paulh002/ESP32Controler/FreeSansOblique.cpp

#include "lvgl.h"

/*******************************************************************************
 * Size: 42 px
 * Bpp: 1
 * Opts: 
 ******************************************************************************/

#ifndef FREESANSOBLIQUE
#define FREESANSOBLIQUE 1
#endif

#if FREESANSOBLIQUE

/*-----------------
 *    BITMAPS
 *----------------*/

/*Store the image of the glyphs*/
static LV_ATTRIBUTE_LARGE_CONST const uint8_t gylph_bitmap[] = {
    /* U+2C "," */
    0x3e, 0x7c, 0xf1, 0xe0, 0xc1, 0x82, 0xc, 0x31,
    0xc0,

    /* U+2E "." */
    0xff, 0xfd, 0xe0,

    /* U+30 "0" */
    0x0, 0x1f, 0x80, 0x7, 0xfe, 0x0, 0x7f, 0xf8,
    0x7, 0xc3, 0xe0, 0x78, 0xf, 0x83, 0x80, 0x3c,
    0x3c, 0x1, 0xe3, 0xc0, 0xf, 0x1e, 0x0, 0x78,
    0xe0, 0x3, 0xcf, 0x0, 0x1e, 0x78, 0x0, 0xf3,
    0x80, 0x7, 0xbc, 0x0, 0x3d, 0xe0, 0x1, 0xef,
    0x0, 0xe, 0x70, 0x0, 0xf3, 0x80, 0x7, 0xbc,
    0x0, 0x3d, 0xe0, 0x1, 0xcf, 0x0, 0x1e, 0x78,
    0x0, 0xf3, 0xc0, 0xf, 0x1e, 0x0, 0x78, 0xf0,
    0x7, 0x87, 0x80, 0x3c, 0x1e, 0x3, 0xc0, 0xf8,
    0x7c, 0x3, 0xff, 0xc0, 0xf, 0xfc, 0x0, 0x1f,
    0x80, 0x0,

    /* U+31 "1" */
    0x0, 0x70, 0x7, 0x0, 0xf0, 0xe, 0x1, 0xe0,
    0x7e, 0x3f, 0xef, 0xfc, 0xff, 0xcf, 0xfc, 0x3,
    0xc0, 0x3c, 0x3, 0x80, 0x38, 0x7, 0x80, 0x78,
    0x7, 0x80, 0x70, 0xf, 0x0, 0xf0, 0xf, 0x0,
    0xf0, 0xe, 0x1, 0xe0, 0x1e, 0x1, 0xe0, 0x1e,
    0x1, 0xc0, 0x3c, 0x3, 0xc0, 0x3c, 0x0,

    /* U+32 "2" */
    0x0, 0x7, 0xf0, 0x0, 0xf, 0xfe, 0x0, 0x1f,
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
    0x0, 0x0, 0x78, 0x0, 0x3, 0xc0, 0x0, 0x1e,
    0x0, 0x0, 0xf0, 0x0, 0x7, 0x80, 0x0, 0x3c,
    0x0, 0x1, 0xe0, 0x0, 0xf, 0x0, 0x0, 0xf8,
    0x0, 0x7, 0xc0, 0x0, 0x1f, 0xff, 0xf8, 0x7f,
    0xff, 0xe3, 0xff, 0xff, 0x0
};


/*---------------------
 *  GLYPH DESCRIPTION
 *--------------------*/

static const lv_font_fmt_txt_glyph_dsc_t glyph_dsc[] = {
    {.bitmap_index = 0, .adv_w = 0, .box_w = 0, .box_h = 0, .ofs_x = 0, .ofs_y = 0} /* id = 0 reserved */,
    {.bitmap_index = 0, .adv_w = 187, .box_w = 7, .box_h = 10, .ofs_x = 2, .ofs_y = -6},
    {.bitmap_index = 9, .adv_w = 187, .box_w = 5, .box_h = 4, .ofs_x = 4, .ofs_y = 0},
    {.bitmap_index = 12, .adv_w = 374, .box_w = 21, .box_h = 31, .ofs_x = 4, .ofs_y = -1},
    {.bitmap_index = 94, .adv_w = 374, .box_w = 12, .box_h = 31, .ofs_x = 9, .ofs_y = 0},
    {.bitmap_index = 141, .adv_w = 374, .box_w = 25, .box_h = 30, .ofs_x = 1, .ofs_y = 0},
    {.bitmap_index = 235, .adv_w = 374, .box_w = 22, .box_h = 31, .ofs_x = 3, .ofs_y = -1},
    {.bitmap_index = 321, .adv_w = 374, .box_w = 21, .box_h = 30, .ofs_x = 3, .ofs_y = 0},
    {.bitmap_index = 400, .adv_w = 374, .box_w = 23, .box_h = 31, .ofs_x = 3, .ofs_y = -1},
    {.bitmap_index = 490, .adv_w = 374, .box_w = 22, .box_h = 31, .ofs_x = 4, .ofs_y = -1},
    {.bitmap_index = 576, .adv_w = 374, .box_w = 22, .box_h = 30, .ofs_x = 6, .ofs_y = 0},
    {.bitmap_index = 659, .adv_w = 374, .box_w = 22, .box_h = 31, .ofs_x = 3, .ofs_y = -1},
    {.bitmap_index = 745, .adv_w = 374, .box_w = 22, .box_h = 31, .ofs_x = 3, .ofs_y = -1},
    {.bitmap_index = 831, .adv_w = 560, .box_w = 35, .box_h = 31, .ofs_x = 3, .ofs_y = 0},
    {.bitmap_index = 967, .adv_w = 374, .box_w = 21, .box_h = 32, .ofs_x = 3, .ofs_y = -1},
    {.bitmap_index = 1051, .adv_w = 336, .box_w = 22, .box_h = 22, .ofs_x = 1, .ofs_y = 0}
};

/*---------------------
 *  CHARACTER MAPPING
 *--------------------*/

static const uint16_t unicode_list_0[] = {
    0x0, 0x2, 0x4, 0x5, 0x6, 0x7, 0x8, 0x9,
    0xa, 0xb, 0xc, 0xd, 0x21, 0x3c, 0x4e
};

/*Collect the unicode lists and glyph_id offsets*/
static const lv_font_fmt_txt_cmap_t cmaps[] =
{
    {
        .range_start = 44, .range_length = 79, .glyph_id_start = 1,
        .unicode_list = unicode_list_0, .glyph_id_ofs_list = NULL, .list_length = 15, .type = LV_FONT_FMT_TXT_CMAP_SPARSE_TINY
    }
};

/*-----------------
 *    KERNING
 *----------------*/


/*Pair left and right glyphs for kerning*/
static const uint8_t kern_pair_glyph_ids[] =
{
    14, 15,
    15, 15
};

/* Kerning between the respective left and right glyphs
 * 4.4 format which needs to scaled with `kern_scale`*/
static const int8_t kern_pair_values[] =
{
    -17, -20
};

/*Collect the kern pair's data in one place*/
static const lv_font_fmt_txt_kern_pair_t kern_pairs =
{
    .glyph_ids = kern_pair_glyph_ids,
    .values = kern_pair_values,
    .pair_cnt = 2,
    .glyph_ids_size = 0
};

/*--------------------
 *  ALL CUSTOM DATA
 *--------------------*/

/*Store all the custom data of the font*/
static lv_font_fmt_txt_dsc_t font_dsc = {
    .glyph_bitmap = gylph_bitmap,
    .glyph_dsc = glyph_dsc,
    .cmaps = cmaps,
    .kern_dsc = &kern_pairs,
    .kern_scale = 16,
    .cmap_num = 1,
    .bpp = 1,
    .kern_classes = 0,
    .bitmap_format = 0
};


/*-----------------
 *  PUBLIC FONT
 *----------------*/

/*Initialize a public general font descriptor*/
lv_font_t FreeSansOblique = {
    .get_glyph_dsc = lv_font_get_glyph_dsc_fmt_txt,    /*Function pointer to get glyph's data*/
    .get_glyph_bitmap = lv_font_get_bitmap_fmt_txt,    /*Function pointer to get glyph's bitmap*/
    .line_height = 37,          /*The maximum line height required by the font*/
    .base_line = 6,             /*Baseline measured from the bottom of the line*/
#if !(LVGL_VERSION_MAJOR == 6 && LVGL_VERSION_MINOR == 0)
    .subpx = LV_FONT_SUBPX_NONE,
#endif
#if LV_VERSION_CHECK(7, 4, 0)
    .underline_position = -7,
    .underline_thickness = 2,
#endif
    .dsc = &font_dsc           /*The custom font data. Will be accessed by `get_glyph_bitmap/dsc` */
};



#endif /*#if FREESANSOBLIQUE*/
