paulh002/ESP32Controler/FreeSansOblique24.c

/*******************************************************************************
 * Size: 24 px
 * Bpp: 1
 * Opts: 
 ******************************************************************************/

#ifdef LV_LVGL_H_INCLUDE_SIMPLE
#include "lvgl.h"
#else
#include "lvgl.h"
#endif

#ifndef FREESANSOBLIQUE24
#define FREESANSOBLIQUE24 1
#endif

#if FREESANSOBLIQUE24

/*-----------------
 *    BITMAPS
 *----------------*/

/*Store the image of the glyphs*/
static LV_ATTRIBUTE_LARGE_CONST const uint8_t glyph_bitmap[] = {
    /* U+002C "," */
    0x77, 0x32, 0x2c,

    /* U+002E "." */
    0xfc,

    /* U+002F "/" */
    0x0, 0x40, 0x30, 0x8, 0x6, 0x1, 0x0, 0xc0,
    0x20, 0x18, 0x4, 0x2, 0x0, 0x80, 0x40, 0x10,
    0x8, 0x2, 0x1, 0x0, 0xc0, 0x20, 0x0,

    /* U+0030 "0" */
    0x3, 0xc0, 0xfe, 0x1c, 0x71, 0x83, 0x30, 0x33,
    0x3, 0x70, 0x36, 0x3, 0x60, 0x36, 0x3, 0x60,
    0x7e, 0x6, 0xe0, 0x6c, 0xe, 0xe0, 0xc6, 0x1c,
    0x7f, 0x83, 0xf0, 0x8, 0x0,

    /* U+0031 "1" */
    0x6, 0xc, 0x33, 0xef, 0xc1, 0x83, 0xc, 0x18,
    0x30, 0x60, 0xc3, 0x6, 0xc, 0x18, 0x70, 0xc0,

    /* U+0032 "2" */
    0x3, 0xf0, 0x1f, 0xe0, 0xe1, 0x87, 0x7, 0x18,
    0xc, 0x60, 0x30, 0x1, 0x80, 0xe, 0x0, 0x70,
    0x7, 0x80, 0x3c, 0x3, 0xc0, 0x1c, 0x0, 0xe0,
    0x6, 0x0, 0x18, 0x0, 0xff, 0xe3, 0xff, 0x80,

    /* U+0033 "3" */
    0x7, 0xc0, 0xff, 0x1c, 0x73, 0x83, 0x30, 0x33,
    0x3, 0x0, 0x30, 0xe, 0x7, 0xc0, 0x7c, 0x0,
    0xe0, 0x6, 0x0, 0x6c, 0x6, 0xc0, 0x6c, 0xc,
    0xff, 0x87, 0xf0, 0x8, 0x0,

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
    0xcc, 0x6c, 0xe6, 0x36, 0x63, 0x33, 0x71, 0x99,
    0xb0, 0xd8, 0xd8, 0x2c, 0x78, 0x1c, 0x3c, 0xe,
    0x1c, 0x6, 0xe, 0x0,

    /* U+0078 "x" */
    0xc, 0x1c, 0x30, 0xe0, 0xe3, 0x1, 0x98, 0x7,
    0xc0, 0xe, 0x0, 0x30, 0x1, 0xe0, 0xf, 0x80,
    0x73, 0x1, 0x8c, 0xc, 0x38, 0x60, 0x60,

    /* U+0079 "y" */
    0x18, 0xc, 0x70, 0x61, 0xc1, 0x83, 0xc, 0xc,
    0x70, 0x31, 0x80, 0xcc, 0x3, 0x30, 0xd, 0x80,
    0x36, 0x0, 0x70, 0x1, 0xc0, 0x6, 0x0, 0x30,
    0x0, 0xc0, 0x6, 0x0, 0xf8, 0x3, 0x80, 0x0,

    /* U+007A "z" */
    0x1f, 0xf1, 0xff, 0x0, 0x60, 0xc, 0x1, 0x80,
    0x30, 0x6, 0x0, 0xc0, 0x18, 0x3, 0x0, 0x60,
    0xf, 0xfc, 0xff, 0xc0
};


/*---------------------
 *  GLYPH DESCRIPTION
 *--------------------*/

static const lv_font_fmt_txt_glyph_dsc_t glyph_dsc[] = {
    {.bitmap_index = 0, .adv_w = 0, .box_w = 0, .box_h = 0, .ofs_x = 0, .ofs_y = 0} /* id = 0 reserved */,
    {.bitmap_index = 0, .adv_w = 107, .box_w = 4, .box_h = 6, .ofs_x = 1, .ofs_y = -4},
    {.bitmap_index = 3, .adv_w = 107, .box_w = 3, .box_h = 2, .ofs_x = 2, .ofs_y = 0},
    {.bitmap_index = 4, .adv_w = 107, .box_w = 10, .box_h = 18, .ofs_x = 0, .ofs_y = 0},
    {.bitmap_index = 27, .adv_w = 214, .box_w = 12, .box_h = 19, .ofs_x = 2, .ofs_y = -1},
    {.bitmap_index = 56, .adv_w = 214, .box_w = 7, .box_h = 18, .ofs_x = 5, .ofs_y = 0},
    {.bitmap_index = 72, .adv_w = 214, .box_w = 14, .box_h = 18, .ofs_x = 1, .ofs_y = 0},
    {.bitmap_index = 104, .adv_w = 214, .box_w = 12, .box_h = 19, .ofs_x = 2, .ofs_y = -1},
    {.bitmap_index = 133, .adv_w = 214, .box_w = 12, .box_h = 18, .ofs_x = 2, .ofs_y = 0},
    {.bitmap_index = 160, .adv_w = 214, .box_w = 13, .box_h = 19, .ofs_x = 2, .ofs_y = -1},
    {.bitmap_index = 191, .adv_w = 214, .box_w = 13, .box_h = 19, .ofs_x = 2, .ofs_y = -1},
    {.bitmap_index = 222, .adv_w = 214, .box_w = 13, .box_h = 18, .ofs_x = 3, .ofs_y = 0},
    {.bitmap_index = 252, .adv_w = 214, .box_w = 13, .box_h = 19, .ofs_x = 2, .ofs_y = -1},
    {.bitmap_index = 283, .adv_w = 214, .box_w = 12, .box_h = 19, .ofs_x = 2, .ofs_y = -1},
    {.bitmap_index = 312, .adv_w = 107, .box_w = 5, .box_h = 13, .ofs_x = 3, .ofs_y = 0},
    {.bitmap_index = 321, .adv_w = 107, .box_w = 6, .box_h = 17, .ofs_x = 2, .ofs_y = -4},
    {.bitmap_index = 334, .adv_w = 224, .box_w = 13, .box_h = 11, .ofs_x = 2, .ofs_y = 0},
    {.bitmap_index = 352, .adv_w = 224, .box_w = 13, .box_h = 11, .ofs_x = 1, .ofs_y = 0},
    {.bitmap_index = 370, .adv_w = 214, .box_w = 11, .box_h = 18, .ofs_x = 4, .ofs_y = 0},
    {.bitmap_index = 395, .adv_w = 256, .box_w = 16, .box_h = 18, .ofs_x = 0, .ofs_y = 0},
    {.bitmap_index = 431, .adv_w = 256, .box_w = 15, .box_h = 18, .ofs_x = 2, .ofs_y = 0},
    {.bitmap_index = 465, .adv_w = 277, .box_w = 15, .box_h = 19, .ofs_x = 3, .ofs_y = -1},
    {.bitmap_index = 501, .adv_w = 277, .box_w = 16, .box_h = 18, .ofs_x = 2, .ofs_y = 0},
    {.bitmap_index = 537, .adv_w = 256, .box_w = 16, .box_h = 18, .ofs_x = 2, .ofs_y = 0},
    {.bitmap_index = 573, .adv_w = 235, .box_w = 16, .box_h = 18, .ofs_x = 2, .ofs_y = 0},
    {.bitmap_index = 609, .adv_w = 299, .box_w = 16, .box_h = 19, .ofs_x = 3, .ofs_y = -1},
    {.bitmap_index = 647, .adv_w = 277, .box_w = 17, .box_h = 18, .ofs_x = 2, .ofs_y = 0},
    {.bitmap_index = 686, .adv_w = 107, .box_w = 6, .box_h = 18, .ofs_x = 2, .ofs_y = 0},
    {.bitmap_index = 700, .adv_w = 192, .box_w = 13, .box_h = 19, .ofs_x = 1, .ofs_y = -1},
    {.bitmap_index = 731, .adv_w = 256, .box_w = 18, .box_h = 18, .ofs_x = 2, .ofs_y = 0},
    {.bitmap_index = 772, .adv_w = 214, .box_w = 11, .box_h = 18, .ofs_x = 2, .ofs_y = 0},
    {.bitmap_index = 797, .adv_w = 320, .box_w = 20, .box_h = 18, .ofs_x = 2, .ofs_y = 0},
    {.bitmap_index = 842, .adv_w = 277, .box_w = 17, .box_h = 18, .ofs_x = 2, .ofs_y = 0},
    {.bitmap_index = 881, .adv_w = 299, .box_w = 18, .box_h = 19, .ofs_x = 2, .ofs_y = -1},
    {.bitmap_index = 924, .adv_w = 256, .box_w = 16, .box_h = 18, .ofs_x = 2, .ofs_y = 0},
    {.bitmap_index = 960, .adv_w = 299, .box_w = 18, .box_h = 19, .ofs_x = 2, .ofs_y = -1},
    {.bitmap_index = 1003, .adv_w = 277, .box_w = 16, .box_h = 18, .ofs_x = 2, .ofs_y = 0},
    {.bitmap_index = 1039, .adv_w = 256, .box_w = 15, .box_h = 19, .ofs_x = 2, .ofs_y = -1},
    {.bitmap_index = 1075, .adv_w = 235, .box_w = 14, .box_h = 18, .ofs_x = 4, .ofs_y = 0},
    {.bitmap_index = 1107, .adv_w = 277, .box_w = 16, .box_h = 19, .ofs_x = 3, .ofs_y = -1},
    {.bitmap_index = 1145, .adv_w = 256, .box_w = 15, .box_h = 18, .ofs_x = 4, .ofs_y = 0},
    {.bitmap_index = 1179, .adv_w = 362, .box_w = 22, .box_h = 18, .ofs_x = 4, .ofs_y = 0},
    {.bitmap_index = 1229, .adv_w = 256, .box_w = 18, .box_h = 18, .ofs_x = 1, .ofs_y = 0},
    {.bitmap_index = 1270, .adv_w = 256, .box_w = 16, .box_h = 18, .ofs_x = 4, .ofs_y = 0},
    {.bitmap_index = 1306, .adv_w = 235, .box_w = 17, .box_h = 18, .ofs_x = 1, .ofs_y = 0},
    {.bitmap_index = 1345, .adv_w = 107, .box_w = 10, .box_h = 23, .ofs_x = 0, .ofs_y = -5},
    {.bitmap_index = 1374, .adv_w = 107, .box_w = 10, .box_h = 23, .ofs_x = -1, .ofs_y = -5},
    {.bitmap_index = 1403, .adv_w = 214, .box_w = 12, .box_h = 14, .ofs_x = 2, .ofs_y = -1},
    {.bitmap_index = 1424, .adv_w = 214, .box_w = 13, .box_h = 19, .ofs_x = 1, .ofs_y = -1},
    {.bitmap_index = 1455, .adv_w = 192, .box_w = 11, .box_h = 14, .ofs_x = 2, .ofs_y = -1},
    {.bitmap_index = 1475, .adv_w = 214, .box_w = 14, .box_h = 19, .ofs_x = 2, .ofs_y = -1},
    {.bitmap_index = 1509, .adv_w = 214, .box_w = 12, .box_h = 14, .ofs_x = 2, .ofs_y = -1},
    {.bitmap_index = 1530, .adv_w = 107, .box_w = 8, .box_h = 18, .ofs_x = 2, .ofs_y = 0},
    {.bitmap_index = 1548, .adv_w = 214, .box_w = 13, .box_h = 18, .ofs_x = 1, .ofs_y = -5},
    {.bitmap_index = 1578, .adv_w = 214, .box_w = 12, .box_h = 18, .ofs_x = 2, .ofs_y = 0},
    {.bitmap_index = 1605, .adv_w = 85, .box_w = 5, .box_h = 18, .ofs_x = 2, .ofs_y = 0},
    {.bitmap_index = 1617, .adv_w = 85, .box_w = 9, .box_h = 23, .ofs_x = -2, .ofs_y = -5},
    {.bitmap_index = 1643, .adv_w = 192, .box_w = 13, .box_h = 18, .ofs_x = 1, .ofs_y = 0},
    {.bitmap_index = 1673, .adv_w = 85, .box_w = 5, .box_h = 18, .ofs_x = 2, .ofs_y = 0},
    {.bitmap_index = 1685, .adv_w = 320, .box_w = 18, .box_h = 13, .ofs_x = 2, .ofs_y = 0},
    {.bitmap_index = 1715, .adv_w = 214, .box_w = 12, .box_h = 13, .ofs_x = 2, .ofs_y = 0},
    {.bitmap_index = 1735, .adv_w = 214, .box_w = 12, .box_h = 14, .ofs_x = 2, .ofs_y = -1},
    {.bitmap_index = 1756, .adv_w = 214, .box_w = 14, .box_h = 18, .ofs_x = 0, .ofs_y = -5},
    {.bitmap_index = 1788, .adv_w = 214, .box_w = 13, .box_h = 18, .ofs_x = 2, .ofs_y = -5},
    {.bitmap_index = 1818, .adv_w = 128, .box_w = 8, .box_h = 13, .ofs_x = 2, .ofs_y = 0},
    {.bitmap_index = 1831, .adv_w = 192, .box_w = 11, .box_h = 14, .ofs_x = 1, .ofs_y = -1},
    {.bitmap_index = 1851, .adv_w = 107, .box_w = 7, .box_h = 17, .ofs_x = 2, .ofs_y = -1},
    {.bitmap_index = 1866, .adv_w = 214, .box_w = 12, .box_h = 14, .ofs_x = 2, .ofs_y = -1},
    {.bitmap_index = 1887, .adv_w = 192, .box_w = 11, .box_h = 13, .ofs_x = 3, .ofs_y = 0},
    {.bitmap_index = 1905, .adv_w = 277, .box_w = 17, .box_h = 13, .ofs_x = 3, .ofs_y = 0},
    {.bitmap_index = 1933, .adv_w = 192, .box_w = 14, .box_h = 13, .ofs_x = 0, .ofs_y = 0},
    {.bitmap_index = 1956, .adv_w = 192, .box_w = 14, .box_h = 18, .ofs_x = 0, .ofs_y = -5},
    {.bitmap_index = 1988, .adv_w = 192, .box_w = 12, .box_h = 13, .ofs_x = 1, .ofs_y = 0}
};

/*---------------------
 *  CHARACTER MAPPING
 *--------------------*/

static const uint8_t glyph_id_ofs_list_0[] = {
    0, 0, 1, 2, 3, 4, 5, 6,
    7, 8, 9, 10, 11, 12, 13, 14,
    15, 0, 16, 17, 0, 18, 19, 20,
    21, 22, 23, 24, 25, 26, 27, 28,
    29, 30, 31, 32, 33, 34, 35, 36,
    37, 38, 39, 40, 41, 42, 43, 44,
    0, 45
};

/*Collect the unicode lists and glyph_id offsets*/
static const lv_font_fmt_txt_cmap_t cmaps[] =
{
    {
        .range_start = 44, .range_length = 50, .glyph_id_start = 1,
        .unicode_list = NULL, .glyph_id_ofs_list = glyph_id_ofs_list_0, .list_length = 50, .type = LV_FONT_FMT_TXT_CMAP_FORMAT0_FULL
    },
    {
        .range_start = 97, .range_length = 26, .glyph_id_start = 47,
        .unicode_list = NULL, .glyph_id_ofs_list = NULL, .list_length = 0, .type = LV_FONT_FMT_TXT_CMAP_FORMAT0_TINY
    }
};

/*-----------------
 *    KERNING
 *----------------*/


/*Map glyph_ids to kern left classes*/
static const uint8_t kern_left_class_mapping[] =
{
    0, 0, 0, 0, 0, 0, 0, 0,
    0, 0, 0, 0, 0, 0, 0, 0,
    0, 0, 0, 1, 2, 3, 3, 4,
    5, 3, 0, 0, 6, 7, 8, 0,
    0, 9, 10, 9, 11, 12, 13, 0,
    14, 14, 7, 14, 7, 0, 0, 15,
    16, 16, 0, 16, 17, 0, 18, 0,
    0, 19, 0, 18, 18, 16, 16, 0,
    20, 21, 22, 0, 23, 23, 19, 23,
    24
};

/*Map glyph_ids to kern right classes*/
static const uint8_t kern_right_class_mapping[] =
{
    0, 0, 0, 0, 0, 0, 0, 0,
    0, 0, 0, 0, 0, 0, 0, 0,
    0, 0, 0, 1, 0, 2, 0, 0,
    0, 2, 0, 0, 3, 0, 0, 0,
    0, 2, 0, 2, 0, 4, 5, 0,
    6, 6, 7, 6, 7, 0, 0, 8,
    0, 9, 9, 9, 10, 8, 0, 0,
    11, 0, 0, 12, 12, 9, 13, 9,
    14, 15, 10, 16, 17, 17, 18, 17,
    12
};

/*Kern values between classes*/
static const int8_t kern_class_values[] =
{
    0, -15, 0, -12, -15, -23, -4, -8,
    -8, -12, 0, -12, -8, -12, -8, -10,
    -12, 0, -12, -12, 0, -8, -19, -19,
    -19, -4, 0, -4, -8, -12, -4, -8,
    -4, -8, -12, -12, -15, -8, 0, -4,
    -15, -19, -15, -8, 0, -8, -12, -12,
    -8, -8, -8, -12, -4, -12, -12, -15,
    -8, -19, -8, -19, -12, -12, -12, -12,
    -12, -15, -8, -12, -8, -17, -15, -12,
    -15, -12, -12, -15, 0, -8, -12, -12,
    -12, -8, -8, -19, -12, -15, -15, -19,
    -4, -15, -12, -12, 0, -12, 0, -19,
    -19, -12, -8, 0, -8, -15, -8, -12,
    -8, -15, -12, -19, 0, -19, 0, -19,
    0, 0, 0, -12, -15, -12, -4, -15,
    -12, -15, -8, -15, -12, -8, 0, -15,
    0, -15, -15, -23, 0, -8, -12, -12,
    -4, -15, 0, -12, -8, -15, -15, 0,
    -12, 0, 0, -8, -15, -15, -19, -8,
    0, 0, 0, -8, -4, -8, 0, -6,
    0, 0, -23, -8, -15, -12, -12, -15,
    -23, -19, -15, 0, 0, -15, -8, -12,
    -12, -15, 0, -15, -4, -4, 0, -8,
    -8, -19, -8, -4, -4, 0, -4, -4,
    -4, -8, -4, -15, -4, 0, -12, -8,
    0, -4, -15, -19, -19, 0, 0, -4,
    -4, -8, -4, -8, 0, -10, -8, -15,
    -19, -15, -15, -15, 0, -4, -15, -15,
    -15, -8, 0, -15, -12, -15, -15, -15,
    -8, -12, -23, -19, -12, -19, 0, 0,
    -12, -19, -19, -8, 0, -23, -15, -23,
    -15, -19, 0, -12, 0, 0, 0, 0,
    0, 0, 0, -4, 0, -4, 0, -4,
    0, -4, -4, -4, -8, -4, 0, 0,
    0, 0, 0, 0, 0, 0, 0, -4,
    0, -4, 0, -4, -4, -2, -4, -8,
    0, 0, 0, 0, 0, 0, 0, -8,
    -8, 0, 0, -4, 0, -4, -8, -2,
    0, -8, 0, 0, 0, 0, 0, 0,
    0, 0, -4, 0, -8, -10, -4, -8,
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
};


/*Collect the kern class' data in one place*/
static const lv_font_fmt_txt_kern_classes_t kern_classes =
{
    .class_pair_values   = kern_class_values,
    .left_class_mapping  = kern_left_class_mapping,
    .right_class_mapping = kern_right_class_mapping,
    .left_class_cnt      = 24,
    .right_class_cnt     = 18,
};

/*--------------------
 *  ALL CUSTOM DATA
 *--------------------*/

#if LV_VERSION_CHECK(8, 0, 0)
/*Store all the custom data of the font*/
static  lv_font_fmt_txt_glyph_cache_t cache;
static const lv_font_fmt_txt_dsc_t font_dsc = {
#else
static lv_font_fmt_txt_dsc_t font_dsc = {
#endif
    .glyph_bitmap = glyph_bitmap,
    .glyph_dsc = glyph_dsc,
    .cmaps = cmaps,
    .kern_dsc = &kern_classes,
    .kern_scale = 16,
    .cmap_num = 2,
    .bpp = 1,
    .kern_classes = 1,
    .bitmap_format = 0,
#if LV_VERSION_CHECK(8, 0, 0)
    .cache = &cache
#endif
};


/*-----------------
 *  PUBLIC FONT
 *----------------*/

/*Initialize a public general font descriptor*/
#if LV_VERSION_CHECK(8, 0, 0)
const lv_font_t FreeSansOblique24 = {
#else
lv_font_t FreeSansOblique24 = {
#endif
    .get_glyph_dsc = lv_font_get_glyph_dsc_fmt_txt,    /*Function pointer to get glyph's data*/
    .get_glyph_bitmap = lv_font_get_bitmap_fmt_txt,    /*Function pointer to get glyph's bitmap*/
    .line_height = 23,          /*The maximum line height required by the font*/
    .base_line = 5,             /*Baseline measured from the bottom of the line*/
#if !(LVGL_VERSION_MAJOR == 6 && LVGL_VERSION_MINOR == 0)
    .subpx = LV_FONT_SUBPX_NONE,
#endif
#if LV_VERSION_CHECK(7, 4, 0) || LVGL_VERSION_MAJOR >= 8
    .underline_position = -4,
    .underline_thickness = 1,
#endif
    .dsc = &font_dsc           /*The custom font data. Will be accessed by `get_glyph_bitmap/dsc` */
};



#endif /*#if FREESANSOBLIQUE24*/
