paulh002/ESP32Controler/FreeSansOblique32.c

/*******************************************************************************
 * Size: 32 px
 * Bpp: 1
 * Opts: 
 ******************************************************************************/

#ifdef LV_LVGL_H_INCLUDE_SIMPLE
#include "lvgl.h"
#else
#include "lvgl.h"
#endif

#ifndef FREESANSOBLIQUE32
#define FREESANSOBLIQUE32 1
#endif

#if FREESANSOBLIQUE32

/*-----------------
 *    BITMAPS
 *----------------*/

/*Store the image of the glyphs*/
static LV_ATTRIBUTE_LARGE_CONST const uint8_t glyph_bitmap[] = {
    /* U+002C "," */
    0x7b, 0xdc, 0x23, 0x11, 0x98,

    /* U+002E "." */
    0xfe, 0xe0,

    /* U+002F "/" */
    0x0, 0xc, 0x0, 0x60, 0x1, 0x80, 0xc, 0x0,
    0x30, 0x1, 0x80, 0x4, 0x0, 0x30, 0x0, 0x80,
    0x6, 0x0, 0x10, 0x0, 0xc0, 0x6, 0x0, 0x18,
    0x0, 0xc0, 0x3, 0x0, 0x18, 0x0, 0x60, 0x3,
    0x0, 0xc, 0x0, 0x60, 0x1, 0x0, 0xc, 0x0,
    0x20, 0x0,

    /* U+0030 "0" */
    0x0, 0xf8, 0x3, 0xfe, 0x7, 0xe, 0xe, 0x7,
    0x1c, 0x7, 0x18, 0x7, 0x38, 0x7, 0x38, 0x7,
    0x70, 0x7, 0x70, 0x7, 0x70, 0x7, 0x70, 0x6,
    0x60, 0xe, 0xe0, 0xe, 0xe0, 0xe, 0xe0, 0x1c,
    0xe0, 0x1c, 0xe0, 0x18, 0xe0, 0x38, 0x70, 0x70,
    0x7f, 0xe0, 0x3f, 0xc0, 0x4, 0x0,

    /* U+0031 "1" */
    0x1, 0x80, 0xc0, 0xe0, 0xe1, 0xf7, 0xfb, 0xfc,
    0xc, 0xe, 0x7, 0x3, 0x81, 0xc0, 0xc0, 0xe0,
    0x70, 0x38, 0x1c, 0x1c, 0xe, 0x7, 0x3, 0x81,
    0x81, 0xc0,

    /* U+0032 "2" */
    0x0, 0x7f, 0x0, 0x3f, 0xf0, 0xf, 0xf, 0x3,
    0x80, 0xf0, 0x70, 0xe, 0x1c, 0x1, 0xc3, 0x80,
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
    0xc0, 0x1, 0xc0, 0x1, 0xc0, 0x1, 0xc0, 0x1,
    0xc0, 0x1, 0xc0, 0x1, 0xc0, 0x1, 0xc0, 0x1,
    0xc0, 0x1, 0xc0, 0x1, 0xc0, 0x1, 0xc0, 0x1,
    0xff, 0xf8, 0xff, 0xfc, 0x0
};


/*---------------------
 *  GLYPH DESCRIPTION
 *--------------------*/

static const lv_font_fmt_txt_glyph_dsc_t glyph_dsc[] = {
    {.bitmap_index = 0, .adv_w = 0, .box_w = 0, .box_h = 0, .ofs_x = 0, .ofs_y = 0} /* id = 0 reserved */,
    {.bitmap_index = 0, .adv_w = 142, .box_w = 5, .box_h = 8, .ofs_x = 2, .ofs_y = -5},
    {.bitmap_index = 5, .adv_w = 142, .box_w = 4, .box_h = 3, .ofs_x = 3, .ofs_y = 0},
    {.bitmap_index = 7, .adv_w = 142, .box_w = 14, .box_h = 24, .ofs_x = 0, .ofs_y = -1},
    {.bitmap_index = 49, .adv_w = 285, .box_w = 16, .box_h = 23, .ofs_x = 3, .ofs_y = -1},
    {.bitmap_index = 95, .adv_w = 285, .box_w = 9, .box_h = 23, .ofs_x = 7, .ofs_y = 0},
    {.bitmap_index = 121, .adv_w = 285, .box_w = 19, .box_h = 22, .ofs_x = 1, .ofs_y = 0},
    {.bitmap_index = 174, .adv_w = 285, .box_w = 17, .box_h = 23, .ofs_x = 2, .ofs_y = -1},
    {.bitmap_index = 223, .adv_w = 285, .box_w = 16, .box_h = 23, .ofs_x = 2, .ofs_y = 0},
    {.bitmap_index = 269, .adv_w = 285, .box_w = 18, .box_h = 24, .ofs_x = 2, .ofs_y = -1},
    {.bitmap_index = 323, .adv_w = 285, .box_w = 17, .box_h = 23, .ofs_x = 3, .ofs_y = -1},
    {.bitmap_index = 372, .adv_w = 285, .box_w = 17, .box_h = 22, .ofs_x = 4, .ofs_y = 0},
    {.bitmap_index = 419, .adv_w = 285, .box_w = 17, .box_h = 23, .ofs_x = 2, .ofs_y = -1},
    {.bitmap_index = 468, .adv_w = 285, .box_w = 16, .box_h = 23, .ofs_x = 3, .ofs_y = -1},
    {.bitmap_index = 514, .adv_w = 142, .box_w = 6, .box_h = 17, .ofs_x = 4, .ofs_y = 0},
    {.bitmap_index = 527, .adv_w = 142, .box_w = 8, .box_h = 22, .ofs_x = 2, .ofs_y = -5},
    {.bitmap_index = 549, .adv_w = 299, .box_w = 17, .box_h = 15, .ofs_x = 3, .ofs_y = 0},
    {.bitmap_index = 581, .adv_w = 299, .box_w = 17, .box_h = 15, .ofs_x = 2, .ofs_y = 0},
    {.bitmap_index = 613, .adv_w = 285, .box_w = 14, .box_h = 23, .ofs_x = 6, .ofs_y = 0},
    {.bitmap_index = 654, .adv_w = 342, .box_w = 20, .box_h = 23, .ofs_x = 1, .ofs_y = 0},
    {.bitmap_index = 712, .adv_w = 342, .box_w = 20, .box_h = 23, .ofs_x = 3, .ofs_y = 0},
    {.bitmap_index = 770, .adv_w = 370, .box_w = 21, .box_h = 24, .ofs_x = 4, .ofs_y = -1},
    {.bitmap_index = 833, .adv_w = 370, .box_w = 21, .box_h = 23, .ofs_x = 3, .ofs_y = 0},
    {.bitmap_index = 894, .adv_w = 342, .box_w = 21, .box_h = 23, .ofs_x = 3, .ofs_y = 0},
    {.bitmap_index = 955, .adv_w = 313, .box_w = 20, .box_h = 23, .ofs_x = 3, .ofs_y = 0},
    {.bitmap_index = 1013, .adv_w = 398, .box_w = 23, .box_h = 24, .ofs_x = 3, .ofs_y = -1},
    {.bitmap_index = 1082, .adv_w = 370, .box_w = 23, .box_h = 23, .ofs_x = 3, .ofs_y = 0},
    {.bitmap_index = 1149, .adv_w = 142, .box_w = 8, .box_h = 23, .ofs_x = 3, .ofs_y = 0},
    {.bitmap_index = 1172, .adv_w = 256, .box_w = 18, .box_h = 24, .ofs_x = 1, .ofs_y = -1},
    {.bitmap_index = 1226, .adv_w = 342, .box_w = 23, .box_h = 23, .ofs_x = 3, .ofs_y = 0},
    {.bitmap_index = 1293, .adv_w = 285, .box_w = 15, .box_h = 23, .ofs_x = 3, .ofs_y = 0},
    {.bitmap_index = 1337, .adv_w = 426, .box_w = 27, .box_h = 23, .ofs_x = 2, .ofs_y = 0},
    {.bitmap_index = 1415, .adv_w = 370, .box_w = 24, .box_h = 23, .ofs_x = 2, .ofs_y = 0},
    {.bitmap_index = 1484, .adv_w = 398, .box_w = 24, .box_h = 24, .ofs_x = 3, .ofs_y = -1},
    {.bitmap_index = 1556, .adv_w = 342, .box_w = 20, .box_h = 23, .ofs_x = 3, .ofs_y = 0},
    {.bitmap_index = 1614, .adv_w = 398, .box_w = 24, .box_h = 25, .ofs_x = 3, .ofs_y = -2},
    {.bitmap_index = 1689, .adv_w = 370, .box_w = 22, .box_h = 23, .ofs_x = 3, .ofs_y = 0},
    {.bitmap_index = 1753, .adv_w = 342, .box_w = 20, .box_h = 24, .ofs_x = 3, .ofs_y = -1},
    {.bitmap_index = 1813, .adv_w = 313, .box_w = 19, .box_h = 23, .ofs_x = 5, .ofs_y = 0},
    {.bitmap_index = 1868, .adv_w = 370, .box_w = 22, .box_h = 24, .ofs_x = 4, .ofs_y = -1},
    {.bitmap_index = 1934, .adv_w = 342, .box_w = 20, .box_h = 23, .ofs_x = 6, .ofs_y = 0},
    {.bitmap_index = 1992, .adv_w = 483, .box_w = 29, .box_h = 23, .ofs_x = 6, .ofs_y = 0},
    {.bitmap_index = 2076, .adv_w = 342, .box_w = 24, .box_h = 23, .ofs_x = 1, .ofs_y = 0},
    {.bitmap_index = 2145, .adv_w = 342, .box_w = 21, .box_h = 23, .ofs_x = 5, .ofs_y = 0},
    {.bitmap_index = 2206, .adv_w = 313, .box_w = 23, .box_h = 23, .ofs_x = 1, .ofs_y = 0},
    {.bitmap_index = 2273, .adv_w = 142, .box_w = 12, .box_h = 30, .ofs_x = 1, .ofs_y = -7},
    {.bitmap_index = 2318, .adv_w = 142, .box_w = 13, .box_h = 30, .ofs_x = -1, .ofs_y = -7},
    {.bitmap_index = 2367, .adv_w = 285, .box_w = 16, .box_h = 18, .ofs_x = 2, .ofs_y = -1},
    {.bitmap_index = 2403, .adv_w = 285, .box_w = 17, .box_h = 24, .ofs_x = 2, .ofs_y = -1},
    {.bitmap_index = 2454, .adv_w = 256, .box_w = 16, .box_h = 18, .ofs_x = 2, .ofs_y = -1},
    {.bitmap_index = 2490, .adv_w = 285, .box_w = 19, .box_h = 24, .ofs_x = 2, .ofs_y = -1},
    {.bitmap_index = 2547, .adv_w = 285, .box_w = 16, .box_h = 18, .ofs_x = 3, .ofs_y = -1},
    {.bitmap_index = 2583, .adv_w = 142, .box_w = 10, .box_h = 23, .ofs_x = 3, .ofs_y = 0},
    {.bitmap_index = 2612, .adv_w = 285, .box_w = 18, .box_h = 24, .ofs_x = 1, .ofs_y = -7},
    {.bitmap_index = 2666, .adv_w = 285, .box_w = 16, .box_h = 23, .ofs_x = 2, .ofs_y = 0},
    {.bitmap_index = 2712, .adv_w = 114, .box_w = 8, .box_h = 23, .ofs_x = 2, .ofs_y = 0},
    {.bitmap_index = 2735, .adv_w = 114, .box_w = 12, .box_h = 30, .ofs_x = -2, .ofs_y = -7},
    {.bitmap_index = 2780, .adv_w = 256, .box_w = 17, .box_h = 23, .ofs_x = 2, .ofs_y = 0},
    {.bitmap_index = 2829, .adv_w = 114, .box_w = 8, .box_h = 23, .ofs_x = 2, .ofs_y = 0},
    {.bitmap_index = 2852, .adv_w = 426, .box_w = 25, .box_h = 17, .ofs_x = 2, .ofs_y = 0},
    {.bitmap_index = 2906, .adv_w = 285, .box_w = 16, .box_h = 17, .ofs_x = 2, .ofs_y = 0},
    {.bitmap_index = 2940, .adv_w = 285, .box_w = 15, .box_h = 18, .ofs_x = 3, .ofs_y = -1},
    {.bitmap_index = 2974, .adv_w = 285, .box_w = 19, .box_h = 24, .ofs_x = 0, .ofs_y = -7},
    {.bitmap_index = 3031, .adv_w = 285, .box_w = 17, .box_h = 24, .ofs_x = 2, .ofs_y = -7},
    {.bitmap_index = 3082, .adv_w = 170, .box_w = 12, .box_h = 17, .ofs_x = 2, .ofs_y = 0},
    {.bitmap_index = 3108, .adv_w = 256, .box_w = 15, .box_h = 18, .ofs_x = 2, .ofs_y = -1},
    {.bitmap_index = 3142, .adv_w = 142, .box_w = 9, .box_h = 23, .ofs_x = 3, .ofs_y = -1},
    {.bitmap_index = 3168, .adv_w = 285, .box_w = 16, .box_h = 18, .ofs_x = 3, .ofs_y = -1},
    {.bitmap_index = 3204, .adv_w = 256, .box_w = 15, .box_h = 17, .ofs_x = 4, .ofs_y = 0},
    {.bitmap_index = 3236, .adv_w = 370, .box_w = 22, .box_h = 17, .ofs_x = 4, .ofs_y = 0},
    {.bitmap_index = 3283, .adv_w = 256, .box_w = 18, .box_h = 17, .ofs_x = 1, .ofs_y = 0},
    {.bitmap_index = 3322, .adv_w = 256, .box_w = 19, .box_h = 24, .ofs_x = 0, .ofs_y = -7},
    {.bitmap_index = 3379, .adv_w = 256, .box_w = 17, .box_h = 17, .ofs_x = 1, .ofs_y = 0}
};

/*---------------------
 *  CHARACTER MAPPING
 *--------------------*/

static const uint8_t glyph_id_ofs_list_0[] = {
    0, 0, 1, 2, 3, 4, 5, 6,
    7, 8, 9, 10, 11, 12, 13, 14,
    15, 0, 16, 17, 0, 18, 19, 20,
    21, 22, 23, 24, 25, 26, 27, 28,
    29, 30, 31, 32, 33, 34, 35, 36,
    37, 38, 39, 40, 41, 42, 43, 44,
    0, 45
};

/*Collect the unicode lists and glyph_id offsets*/
static const lv_font_fmt_txt_cmap_t cmaps[] =
{
    {
        .range_start = 44, .range_length = 50, .glyph_id_start = 1,
        .unicode_list = NULL, .glyph_id_ofs_list = glyph_id_ofs_list_0, .list_length = 50, .type = LV_FONT_FMT_TXT_CMAP_FORMAT0_FULL
    },
    {
        .range_start = 97, .range_length = 26, .glyph_id_start = 47,
        .unicode_list = NULL, .glyph_id_ofs_list = NULL, .list_length = 0, .type = LV_FONT_FMT_TXT_CMAP_FORMAT0_TINY
    }
};

/*-----------------
 *    KERNING
 *----------------*/


/*Map glyph_ids to kern left classes*/
static const uint8_t kern_left_class_mapping[] =
{
    0, 0, 0, 0, 0, 0, 0, 0,
    0, 0, 0, 0, 0, 0, 0, 0,
    0, 0, 0, 1, 2, 3, 3, 4,
    5, 3, 0, 0, 6, 7, 8, 0,
    0, 9, 10, 9, 11, 12, 13, 0,
    14, 14, 7, 14, 7, 0, 0, 15,
    16, 16, 0, 16, 17, 0, 18, 0,
    0, 19, 0, 18, 18, 16, 16, 0,
    20, 21, 22, 0, 23, 23, 19, 23,
    24
};

/*Map glyph_ids to kern right classes*/
static const uint8_t kern_right_class_mapping[] =
{
    0, 0, 0, 0, 0, 0, 0, 0,
    0, 0, 0, 0, 0, 0, 0, 0,
    0, 0, 0, 1, 0, 2, 0, 0,
    0, 2, 0, 0, 3, 0, 0, 0,
    0, 2, 0, 2, 0, 4, 5, 0,
    6, 6, 7, 6, 7, 0, 0, 8,
    0, 9, 9, 9, 10, 8, 0, 0,
    11, 0, 0, 12, 12, 9, 13, 9,
    14, 15, 10, 16, 17, 17, 18, 17,
    12
};

/*Kern values between classes*/
static const int8_t kern_class_values[] =
{
    0, -20, 0, -15, -20, -31, -5, -10,
    -10, -15, 0, -15, -10, -15, -10, -13,
    -15, 0, -15, -15, 0, -10, -26, -26,
    -26, -5, 0, -5, -10, -15, -5, -10,
    -5, -10, -15, -15, -20, -10, 0, -5,
    -20, -26, -20, -10, 0, -10, -15, -15,
    -10, -10, -10, -15, -5, -15, -15, -20,
    -10, -26, -10, -26, -15, -15, -15, -15,
    -15, -20, -10, -15, -10, -23, -20, -15,
    -20, -15, -15, -20, 0, -10, -15, -15,
    -15, -10, -10, -26, -15, -20, -20, -26,
    -5, -20, -15, -15, 0, -15, 0, -26,
    -26, -15, -10, 0, -10, -20, -10, -15,
    -10, -20, -15, -26, 0, -26, 0, -26,
    0, 0, 0, -15, -20, -15, -5, -20,
    -15, -20, -10, -20, -15, -10, 0, -20,
    0, -20, -20, -31, 0, -10, -15, -15,
    -5, -20, 0, -15, -10, -20, -20, 0,
    -15, 0, 0, -10, -20, -20, -26, -10,
    0, 0, 0, -10, -5, -10, 0, -8,
    0, 0, -31, -10, -20, -15, -15, -20,
    -31, -26, -20, 0, 0, -20, -10, -15,
    -15, -20, 0, -20, -5, -5, 0, -10,
    -10, -26, -10, -5, -5, 0, -5, -5,
    -5, -10, -5, -20, -5, 0, -15, -10,
    0, -5, -20, -26, -26, 0, 0, -5,
    -5, -10, -5, -10, 0, -13, -10, -20,
    -26, -20, -20, -20, 0, -5, -20, -20,
    -20, -10, 0, -20, -15, -20, -20, -20,
    -10, -15, -31, -26, -15, -26, 0, 0,
    -15, -26, -26, -10, 0, -31, -20, -31,
    -20, -26, 0, -15, 0, 0, 0, 0,
    0, 0, 0, -5, 0, -5, 0, -5,
    0, -5, -5, -5, -10, -5, 0, 0,
    0, 0, 0, 0, 0, 0, 0, -5,
    0, -5, 0, -5, -5, -3, -5, -10,
    0, 0, 0, 0, 0, 0, 0, -10,
    -10, 0, 0, -5, 0, -5, -10, -3,
    0, -10, 0, 0, 0, 0, 0, 0,
    0, 0, -5, 0, -10, -13, -5, -10,
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
};


/*Collect the kern class' data in one place*/
static const lv_font_fmt_txt_kern_classes_t kern_classes =
{
    .class_pair_values   = kern_class_values,
    .left_class_mapping  = kern_left_class_mapping,
    .right_class_mapping = kern_right_class_mapping,
    .left_class_cnt      = 24,
    .right_class_cnt     = 18,
};

/*--------------------
 *  ALL CUSTOM DATA
 *--------------------*/

#if LV_VERSION_CHECK(8, 0, 0)
/*Store all the custom data of the font*/
static  lv_font_fmt_txt_glyph_cache_t cache;
static const lv_font_fmt_txt_dsc_t font_dsc = {
#else
static lv_font_fmt_txt_dsc_t font_dsc = {
#endif
    .glyph_bitmap = glyph_bitmap,
    .glyph_dsc = glyph_dsc,
    .cmaps = cmaps,
    .kern_dsc = &kern_classes,
    .kern_scale = 16,
    .cmap_num = 2,
    .bpp = 1,
    .kern_classes = 1,
    .bitmap_format = 0,
#if LV_VERSION_CHECK(8, 0, 0)
    .cache = &cache
#endif
};


/*-----------------
 *  PUBLIC FONT
 *----------------*/

/*Initialize a public general font descriptor*/
#if LV_VERSION_CHECK(8, 0, 0)
const lv_font_t FreeSansOblique32 = {
#else
lv_font_t FreeSansOblique32 = {
#endif
    .get_glyph_dsc = lv_font_get_glyph_dsc_fmt_txt,    /*Function pointer to get glyph's data*/
    .get_glyph_bitmap = lv_font_get_bitmap_fmt_txt,    /*Function pointer to get glyph's bitmap*/
    .line_height = 30,          /*The maximum line height required by the font*/
    .base_line = 7,             /*Baseline measured from the bottom of the line*/
#if !(LVGL_VERSION_MAJOR == 6 && LVGL_VERSION_MINOR == 0)
    .subpx = LV_FONT_SUBPX_NONE,
#endif
#if LV_VERSION_CHECK(7, 4, 0) || LVGL_VERSION_MAJOR >= 8
    .underline_position = -6,
    .underline_thickness = 2,
#endif
    .dsc = &font_dsc           /*The custom font data. Will be accessed by `get_glyph_bitmap/dsc` */
};



#endif /*#if FREESANSOBLIQUE32*/
