paulh002/ESP32Controler/indicator_hor.c

#ifdef __has_include
    #if __has_include("lvgl.h")
        #ifndef LV_LVGL_H_INCLUDE_SIMPLE
            #define LV_LVGL_H_INCLUDE_SIMPLE
        #endif
    #endif
#endif

#if defined(LV_LVGL_H_INCLUDE_SIMPLE)
    #include "lvgl.h"
#else
    #include "lvgl/lvgl.h"
#endif


#ifndef LV_ATTRIBUTE_MEM_ALIGN
#define LV_ATTRIBUTE_MEM_ALIGN
#endif

#ifndef LV_ATTRIBUTE_IMG_INDICATOR_HOR
#define LV_ATTRIBUTE_IMG_INDICATOR_HOR
#endif

const LV_ATTRIBUTE_MEM_ALIGN LV_ATTRIBUTE_LARGE_CONST LV_ATTRIBUTE_IMG_INDICATOR_HOR uint8_t indicator_hor_map[] = {
#if LV_COLOR_DEPTH == 1 || LV_COLOR_DEPTH == 8
  /*Pixel format: Red: 3 bit, Green: 3 bit, Blue: 2 bit*/
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
, 0x00, 0x00, 0x62, 0xfd, 0x42, 0xfd, 0x02, 0xfd, 0xe2, 0xfc, 0xa2, 0xfc, 0x00, 0x00, 0x00, 0x00, 0x00, 0x00, 0x00, 0x00, 0x00, 0x00, 0xa2, 0xfb, 0x62, 0xfb, 0x22, 0xfb, 0x02, 0xfb, 0xe2, 0xfa, 0x00, 0x00, 0x00, 0x00, 0x00, 0x00, 0x00, 0x00, 0x00, 0x00, 0xe2, 0xf9, 0xc2, 0xf9, 0xa2, 0xf9, 0x62, 0xf9, 0x42, 0xf9, 0x00, 0x00, 0x00, 0x00, 0x00, 0x00, 0x00, 0x00, 0x00, 0x00, 0xa2, 0xf8, 0x82, 0xf8, 0x82, 0xf8, 0x62, 0xf8, 0x62, 0xf8, 0x00, 0x00, 
  0xf0, 0x57, 0xf0, 0x57, 0xf0, 0x57, 0xf0, 0x57, 0xf0, 0x57, 0xf0, 0x57, 0xf0, 0x57, 0x00, 0x00, 0x00, 0x00, 0x00, 0x00, 0xf0, 0x57, 0xf0, 0x57, 0xf0, 0x57, 0xf0, 0x57, 0xf0, 0x57, 0xf0, 0x57, 0xf0, 0x57, 0x00, 0x00, 0x00, 0x00, 0x00, 0x00, 0xf0, 0x57, 0xf0, 0x57, 0xf0, 0x57, 0xf0, 0x57, 0xf0, 0x57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
  0xf0, 0x57, 0xf0, 0x57, 0xf0, 0x57, 0xf0, 0x57, 0xf0, 0x57, 0xf0, 0x57, 0xf0, 0x57, 0x00, 0x00, 0x00, 0x00, 0x00, 0x00, 0xf0, 0x57, 0xf0, 0x57, 0xf0, 0x57, 0xf0, 0x57, 0xf0, 0x57, 0xf0, 0x57, 0xf0, 0x57, 0x00, 0x00, 0x00, 0x00, 0x00, 0x00, 0xf0, 0x57, 0xf0, 0x57, 0xf0, 0x57, 0xf0, 0x57, 0xf0, 0x57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
  0xf0, 0x57, 0xf0, 0x57, 0xf0, 0x57, 0xf0, 0x57, 0xf0, 0x57, 0xf0, 0x57, 0xf0, 0x57, 0x00, 0x00, 0x00, 0x00, 0x00, 0x00, 0xf0, 0x57, 0xf0, 0x57, 0xf0, 0x57, 0xf0, 0x57, 0xf0, 0x57, 0xf0, 0x57, 0xf0, 0x57, 0x00, 0x00, 0x00, 0x00, 0x00, 0x00, 0xf0, 0x57, 0xf0, 0x57, 0xf0, 0x57, 0xf0, 0x57, 0xf0, 0x57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
  0xf0, 0x57, 0xf0, 0x57, 0xf0, 0x57, 0xf0, 0x57, 0xf0, 0x57, 0xf0, 0x57, 0xf0, 0x57, 0x00, 0x00, 0x00, 0x00, 0x00, 0x00, 0xf0, 0x57, 0xf0, 0x57, 0xf0, 0x57, 0xf0, 0x57, 0xf0, 0x57, 0xf0, 0x57, 0xf0, 0x57, 0x00, 0x00, 0x00, 0x00, 0x00, 0x00, 0xf0, 0x57, 0xf0, 0x57, 0xf0, 0x57, 0xf0, 0x57, 0xf0, 0x57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
  0xf0, 0x57, 0xf0, 0x57, 0xf0, 0x57, 0xf0, 0x57, 0xf0, 0x57, 0xf0, 0x57, 0xf0, 0x57, 0x00, 0x00, 0x00, 0x00, 0x00, 0x00, 0xf0, 0x57, 0xf0, 0x57, 0xf0, 0x57, 0xf0, 0x57, 0xf0, 0x57, 0xf0, 0x57, 0xf0, 0x57, 0x00, 0x00, 0x00, 0x00, 0x00, 0x00, 0xf0, 0x57, 0xf0, 0x57, 0xf0, 0x57, 0xf0, 0x57, 0xf0, 0x57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
  0xf0, 0x57, 0xf0, 0x57, 0xf0, 0x57, 0xf0, 0x57, 0xf0, 0x57, 0xf0, 0x57, 0xf0, 0x57, 0x00, 0x00, 0x00, 0x00, 0x00, 0x00, 0xf0, 0x57, 0xf0, 0x57, 0xf0, 0x57, 0xf0, 0x57, 0xf0, 0x57, 0xf0, 0x57, 0xf0, 0x57, 0x00, 0x00, 0x00, 0x00, 0x00, 0x00, 0xf0, 0x57, 0xf0, 0x57, 0xf0, 0x57, 0xf0, 0x57, 0xf0, 0x57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
  0xf0, 0x57, 0xf0, 0x57, 0xf0, 0x57, 0xf0, 0x57, 0xf0, 0x57, 0xf0, 0x57, 0xf0, 0x57, 0x00, 0x00, 0x00, 0x00, 0x00, 0x00, 0xf0, 0x57, 0xf0, 0x57, 0xf0, 0x57, 0xf0, 0x57, 0xf0, 0x57, 0xf0, 0x57, 0xf0, 0x57, 0x00, 0x00, 0x00, 0x00, 0x00, 0x00, 0xf0, 0x57, 0xf0, 0x57, 0xf0, 0x57, 0xf0, 0x57, 0xf0, 0x57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
  0xf0, 0x57, 0xf0, 0x57, 0xf0, 0x57, 0xf0, 0x57, 0xf0, 0x57, 0xf0, 0x57, 0xf0, 0x57, 0x00, 0x00, 0x00, 0x00, 0x00, 0x00, 0xf0, 0x57, 0xf0, 0x57, 0xf0, 0x57, 0xf0, 0x57, 0xf0, 0x57, 0xf0, 0x57, 0xf0, 0x57, 0x00, 0x00, 0x00, 0x00, 0x00, 0x00, 0xf0, 0x57, 0xf0, 0x57, 0xf0, 0x57, 0xf0, 0x57, 0xf0, 0x57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
  0xf0, 0x57, 0xf0, 0x57, 0xf0, 0x57, 0xf0, 0x57, 0xf0, 0x57, 0xf0, 0x57, 0xf0, 0x57, 0x00, 0x00, 0x00, 0x00, 0x00, 0x00, 0xf0, 0x57, 0xf0, 0x57, 0xf0, 0x57, 0xf0, 0x57, 0xf0, 0x57, 0xf0, 0x57, 0xf0, 0x57, 0x00, 0x00, 0x00, 0x00, 0x00, 0x00, 0xf0, 0x57, 0xf0, 0x57, 0xf0, 0x57, 0xf0, 0x57, 0xf0, 0x57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
  0xf0, 0x57, 0xf0, 0x57, 0xf0, 0x57, 0xf0, 0x57, 0xf0, 0x57, 0xf0, 0x57, 0xf0, 0x57, 0x00, 0x00, 0x00, 0x00, 0x00, 0x00, 0xf0, 0x57, 0xf0, 0x57, 0xf0, 0x57, 0xf0, 0x57, 0xf0, 0x57, 0xf0, 0x57, 0xf0, 0x57, 0x00, 0x00, 0x00, 0x00, 0x00, 0x00, 0xf0, 0x57, 0xf0, 0x57, 0xf0, 0x57, 0xf0, 0x57, 0xf0, 0x57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
  0xf0, 0x57, 0xf0, 0x57, 0xf0, 0x57, 0xf0, 0x57, 0xf0, 0x57, 0xf0, 0x57, 0xf0, 0x57, 0x00, 0x00, 0x00, 0x00, 0x00, 0x00, 0xf0, 0x57, 0xf0, 0x57, 0xf0, 0x57, 0xf0, 0x57, 0xf0, 0x57, 0xf0, 0x57, 0xf0, 0x57, 0x00, 0x00, 0x00, 0x00, 0x00, 0x00, 0xf0, 0x57, 0xf0, 0x57, 0xf0, 0x57, 0xf0, 0x57, 0xf0, 0x57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
  0xf0, 0x57, 0xf0, 0x57, 0xf0, 0x57, 0xf0, 0x57, 0xf0, 0x57, 0xf0, 0x57, 0xf0, 0x57, 0x00, 0x00, 0x00, 0x00, 0x00, 0x00, 0xf0, 0x57, 0xf0, 0x57, 0xf0, 0x57, 0xf0, 0x57, 0xf0, 0x57, 0xf0, 0x57, 0xf0, 0x57, 0x00, 0x00, 0x00, 0x00, 0x00, 0x00, 0xf0, 0x57, 0xf0, 0x57, 0xf0, 0x57, 0xf0, 0x57, 0xf0, 0x57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
  0xf0, 0x57, 0xf0, 0x57, 0xf0, 0x57, 0xf0, 0x57, 0xf0, 0x57, 0xf0, 0x57, 0xf0, 0x57, 0x00, 0x00, 0x00, 0x00, 0x00, 0x00, 0xf0, 0x57, 0xf0, 0x57, 0xf0, 0x57, 0xf0, 0x57, 0xf0, 0x57, 0xf0, 0x57, 0xf0, 0x57, 0x00, 0x00, 0x00, 0x00, 0x00, 0x00, 0xf0, 0x57, 0xf0, 0x57, 0xf0, 0x57, 0xf0, 0x57, 0xf0, 0x57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
  0xf0, 0x57, 0xf0, 0x57, 0xf0, 0x57, 0xf0, 0x57, 0xf0, 0x57, 0xf0, 0x57, 0xf0, 0x57, 0x00, 0x00, 0x00, 0x00, 0x00, 0x00, 0xf0, 0x57, 0xf0, 0x57, 0xf0, 0x57, 0xf0, 0x57, 0xf0, 0x57, 0xf0, 0x57, 0xf0, 0x57, 0x00, 0x00, 0x00, 0x00, 0x00, 0x00, 0xf0, 0x57, 0xf0, 0x57, 0xf0, 0x57, 0xf0, 0x57, 0xf0, 0x57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
  0xf0, 0x57, 0xf0, 0x57, 0xf0, 0x57, 0xf0, 0x57, 0xf0, 0x57, 0xf0, 0x57, 0xf0, 0x57, 0x00, 0x00, 0x00, 0x00, 0x00, 0x00, 0xf0, 0x57, 0xf0, 0x57, 0xf0, 0x57, 0xf0, 0x57, 0xf0, 0x57, 0xf0, 0x57, 0xf0, 0x57, 0x00, 0x00, 0x00, 0x00, 0x00, 0x00, 0xf0, 0x57, 0xf0, 0x57, 0xf0, 0x57, 0xf0, 0x57, 0xf0, 0x57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
  0xf0, 0x57, 0xf0, 0x57, 0xf0, 0x57, 0xf0, 0x57, 0xf0, 0x57, 0xf0, 0x57, 0xf0, 0x57, 0x00, 0x00, 0x00, 0x00, 0x00, 0x00, 0xf0, 0x57, 0xf0, 0x57, 0xf0, 0x57, 0xf0, 0x57, 0xf0, 0x57, 0xf0, 0x57, 0xf0, 0x57, 0x00, 0x00, 0x00, 0x00, 0x00, 0x00, 0xf0, 0x57, 0xf0, 0x57, 0xf0, 0x57, 0xf0, 0x57, 0xf0, 0x57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
  0xf0, 0x57, 0xf0, 0x57, 0xf0, 0x57, 0xf0, 0x57, 0xf0, 0x57, 0xf0, 0x57, 0xf0, 0x57, 0x00, 0x00, 0x00, 0x00, 0x00, 0x00, 0xf0, 0x57, 0xf0, 0x57, 0xf0, 0x57, 0xf0, 0x57, 0xf0, 0x57, 0xf0, 0x57, 0xf0, 0x57, 0x00, 0x00, 0x00, 0x00, 0x00, 0x00, 0xf0, 0x57, 0xf0, 0x57, 0xf0, 0x57, 0xf0, 0x57, 0xf0, 0x57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
  0xf0, 0x57, 0xf0, 0x57, 0xf0, 0x57, 0xf0, 0x57, 0xf0, 0x57, 0xf0, 0x57, 0xf0, 0x57, 0x00, 0x00, 0x00, 0x00, 0x00, 0x00, 0xf0, 0x57, 0xf0, 0x57, 0xf0, 0x57, 0xf0, 0x57, 0xf0, 0x57, 0xf0, 0x57, 0xf0, 0x57, 0x00, 0x00, 0x00, 0x00, 0x00, 0x00, 0xf0, 0x57, 0xf0, 0x57, 0xf0, 0x57, 0xf0, 0x57, 0xf0, 0x57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
  0xf0, 0x57, 0xf0, 0x57, 0xf0, 0x57, 0xf0, 0x57, 0xf0, 0x57, 0xf0, 0x57, 0xf0, 0x57, 0x00, 0x00, 0x00, 0x00, 0x00, 0x00, 0xf0, 0x57, 0xf0, 0x57, 0xf0, 0x57, 0xf0, 0x57, 0xf0, 0x57, 0xf0, 0x57, 0xf0, 0x57, 0x00, 0x00, 0x00, 0x00, 0x00, 0x00, 0xf0, 0x57, 0xf0, 0x57, 0xf0, 0x57, 0xf0, 0x57, 0xf0, 0x57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
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
